Irdroid/authKi/Hardware/Pictures/Hi-Res/PB170094-1.jpg

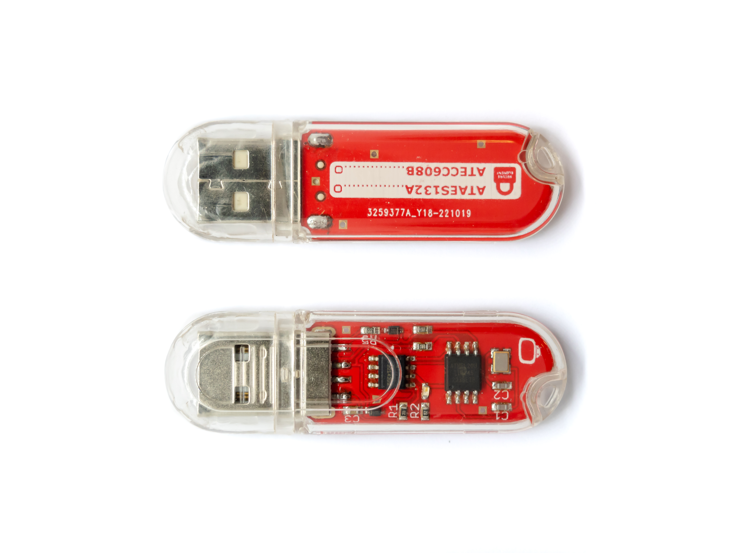
Hardware/Pictures/Hi-Res/PB170094-1.jpg
