Irdroid/authKi/Hardware/Enclosure/3D Model/small plastic instrument enclosure usb stick junction housing abs material pcb enclosure.jpg

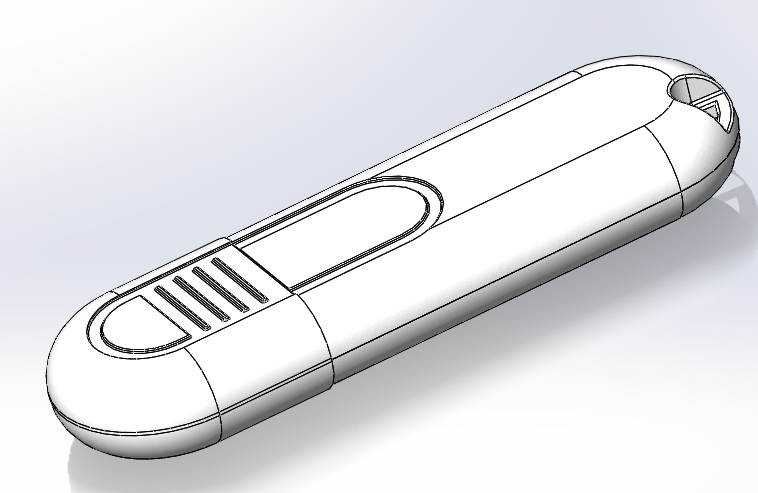
Hardware/Enclosure/3D Model/small plastic instrument enclosure usb stick junction housing abs material pcb enclosure.jpg
